timmy-quinn/hid_keyboard/01_FW/src/kb_ble/kb_cent.c

#include <bluetooth/gatt_dm.h>
#include <bluetooth/scan.h>
#include <bluetooth/services/hogp.h>
#include <errno.h>
#include <stddef.h>
#include <zephyr/bluetooth/bluetooth.h>
#include <zephyr/bluetooth/conn.h>
#include <zephyr/bluetooth/gatt.h>
#include <zephyr/bluetooth/hci.h>
#include <zephyr/bluetooth/uuid.h>
#include <zephyr/kernel.h>
#include <zephyr/settings/settings.h>
#include <zephyr/sys/byteorder.h>
#include <zephyr/sys/printk.h>
#include <zephyr/types.h>

#include "kb_cent.h"
#include "kb_hid_common.h"
#include "kb_periph.h"

static struct bt_conn *default_conn;
static struct bt_hogp hogp;
static struct bt_conn *auth_conn;

static void hids_on_ready(struct k_work *work);
static K_WORK_DEFINE(hids_ready_work, hids_on_ready);

static void scan_filter_match(struct bt_scan_device_info *device_info,
                              struct bt_scan_filter_match *filter_match,
                              bool connectable) {
    char addr[BT_ADDR_LE_STR_LEN];

    if (!filter_match->uuid.match ||
        (filter_match->uuid.count != 1)) {
        printk("Invalid device connected\n");

        return;
    }

    const struct bt_uuid *uuid = filter_match->uuid.uuid[0];

    bt_addr_le_to_str(device_info->recv_info->addr, addr, sizeof(addr));

    printk("Filters matched on UUID 0x%04x.\nAddress: %s connectable: %s\n",
           BT_UUID_16(uuid)->val,
           addr, connectable ? "yes" : "no");
}

static void scan_connecting_error(struct bt_scan_device_info *device_info) {
    printk("Connecting failed\n");
}

static void scan_connecting(struct bt_scan_device_info *device_info, struct bt_conn *conn) {
    default_conn = bt_conn_ref(conn);
}
/** .. include_startingpoint_scan_rst */
static void scan_filter_no_match(struct bt_scan_device_info *device_info,
                                 bool connectable) {
    int err;
    struct bt_conn *conn;
    char addr[BT_ADDR_LE_STR_LEN];

    if (device_info->recv_info->adv_type == BT_GAP_ADV_TYPE_ADV_DIRECT_IND) {
        bt_addr_le_to_str(device_info->recv_info->addr, addr,
                          sizeof(addr));
        printk("Direct advertising received from %s\n", addr);
        bt_scan_stop();

        err = bt_conn_le_create(device_info->recv_info->addr,
                                BT_CONN_LE_CREATE_CONN,
                                device_info->conn_param, &conn);

        if (!err) {
            default_conn = bt_conn_ref(conn);
            bt_conn_unref(conn);
        }
    }
}
/** .. include_endpoint_scan_rst */
BT_SCAN_CB_INIT(scan_cb, scan_filter_match, scan_filter_no_match,
                scan_connecting_error, scan_connecting);

static void discovery_completed_cb(struct bt_gatt_dm *dm,
                                   void *context) {
    int err;

    printk("The discovery procedure succeeded\n");

    bt_gatt_dm_data_print(dm);

    err = bt_hogp_handles_assign(dm, &hogp);
    if (err) {
        printk("Could not init HIDS client object, error: %d\n", err);
    }

    err = bt_gatt_dm_data_release(dm);
    if (err) {
        printk(
            "Could not release the discovery data, error "
            "code: %d\n",
            err);
    }
}

static void discovery_service_not_found_cb(struct bt_conn *conn,
                                           void *context) {
    printk("The service could not be found during the discovery\n");
}

static void discovery_error_found_cb(struct bt_conn *conn,
                                     int err,
                                     void *context) {
    printk("The discovery procedure failed with %d\n", err);
}

static const struct bt_gatt_dm_cb discovery_cb = {
    .completed = discovery_completed_cb,
    .service_not_found = discovery_service_not_found_cb,
    .error_found = discovery_error_found_cb,
};

void cent_gatt_discover(struct bt_conn *conn) {
    int err;

    if (conn != default_conn) {
        return;
    }

    err = bt_gatt_dm_start(conn, BT_UUID_HIDS, &discovery_cb, NULL);
    if (err) {
        printk(
            "could not start the discovery procedure, error "
            "code: %d\n",
            err);
    }
}

void cent_connected(struct bt_conn *conn, uint8_t conn_err) {
    int err;
    char addr[BT_ADDR_LE_STR_LEN];

    bt_addr_le_to_str(bt_conn_get_dst(conn), addr, sizeof(addr));

    if (conn_err) {
        printk("Failed to connect to %s (%u)\n", addr, conn_err);
        if (conn == default_conn) {
            bt_conn_unref(default_conn);
            default_conn = NULL;

            /* This demo doesn't require active scan */
            err = bt_scan_start(BT_SCAN_TYPE_SCAN_ACTIVE);
            if (err) {
                printk("Scanning failed to start (err %d)\n",
                       err);
            }
        }

        return;
    }

    printk("Connected: %s\n", addr);

    err = bt_conn_set_security(conn, BT_SECURITY_L2);
    if (err) {
        printk("Failed to set security: %d\n", err);

        cent_gatt_discover(conn);
    }
}

void cent_disconnected(struct bt_conn *conn, uint8_t reason) {
    char addr[BT_ADDR_LE_STR_LEN];
    int err;

    bt_addr_le_to_str(bt_conn_get_dst(conn), addr, sizeof(addr));

    if (auth_conn) {
        bt_conn_unref(auth_conn);
        auth_conn = NULL;
    }

    printk("Disconnected: %s (reason %u)\n", addr, reason);

    if (bt_hogp_assign_check(&hogp)) {
        printk("HIDS client active - releasing");
        bt_hogp_release(&hogp);
    }

    if (default_conn != conn) {
        return;
    }

    bt_conn_unref(default_conn);
    default_conn = NULL;

    /* This demo doesn't require active scan */
    err = bt_scan_start(BT_SCAN_TYPE_SCAN_ACTIVE);
    if (err) {
        printk("Scanning failed to start (err %d)\n", err);
    }
}

static void security_changed(struct bt_conn *conn, bt_security_t level,
                             enum bt_security_err err) {
    char addr[BT_ADDR_LE_STR_LEN];

    bt_addr_le_to_str(bt_conn_get_dst(conn), addr, sizeof(addr));

    if (!err) {
        printk("Security changed: %s level %u\n", addr, level);
    } else {
        printk("Security failed: %s level %u err %d\n", addr, level,
               err);
    }

    cent_gatt_discover(conn);
}

BT_CONN_CB_DEFINE(conn_callbacks) = {
    .connected = cent_connected,
    .disconnected = cent_disconnected,
    .security_changed = security_changed};

static void scan_init(void) {
    int err;

    struct bt_scan_init_param scan_init = {
        .connect_if_match = 1,
        .scan_param = NULL,
        .conn_param = BT_LE_CONN_PARAM_DEFAULT};

    bt_scan_init(&scan_init);
    bt_scan_cb_register(&scan_cb);

    err = bt_scan_filter_add(BT_SCAN_FILTER_TYPE_UUID, BT_UUID_HIDS);
    if (err) {
        printk("Scanning filters cannot be set (err %d)\n", err);

        return;
    }

    err = bt_scan_filter_enable(BT_SCAN_UUID_FILTER, false);
    if (err) {
        printk("Filters cannot be turned on (err %d)\n", err);
    }
}

static uint8_t hogp_notify_cb(struct bt_hogp *hogp,
                              struct bt_hogp_rep_info *rep,
                              uint8_t err,
                              const uint8_t *data) {
    static kb_state_t kb;
    uint8_t size = bt_hogp_rep_size(rep);

    if (!data) {
        return BT_GATT_ITER_STOP;
    }
    if (size != INPUT_REPORT_KEYS_MAX_LEN) {
        // TODO: Not sure if this is proper behavior
        //  Not sure if it should return STOP or CONTINUE
        return BT_GATT_ITER_STOP;
    }

    for (uint8_t i = 0; i < KEY_PRESS_MAX; i++) {
        kb_hid_key_change(kb.keys_state[i], data[i + KEY_OFFSET_IN_REPORT]);
        kb.keys_state[i] = data[i + KEY_OFFSET_IN_REPORT];
    }

    if (kb.ctrl_keys != data[0]) {
        for (uint8_t i = 0; i < 8; i++) {
            kb_hid_key_change(get_ctrl_scan_code(kb.ctrl_keys, i),
                              get_ctrl_scan_code(data[0], i));
        }
    }
    kb.ctrl_keys = data[0];

    kb_periph_hid_notify();
    return BT_GATT_ITER_CONTINUE;
}

static uint8_t hogp_boot_kbd_report(struct bt_hogp *hogp,
                                    struct bt_hogp_rep_info *rep,
                                    uint8_t err,
                                    const uint8_t *data) {
    uint8_t size = bt_hogp_rep_size(rep);
    uint8_t i;

    if (!data) {
        return BT_GATT_ITER_STOP;
    }
    printk("Notification, keyboard boot, size: %u, data:", size);
    for (i = 0; i < size; ++i) {
        printk(" 0x%x", data[i]);
    }
    printk("\n");

    return BT_GATT_ITER_CONTINUE;
}

static void hogp_ready_cb(struct bt_hogp *hogp) {
    k_work_submit(&hids_ready_work);
}

static void hids_on_ready(struct k_work *work) {
    int err;
    struct bt_hogp_rep_info *rep = NULL;

    printk("HIDS is ready to work\n");

    while (NULL != (rep = bt_hogp_rep_next(&hogp, rep))) {
        if (bt_hogp_rep_type(rep) ==
            BT_HIDS_REPORT_TYPE_INPUT) {
            printk("Subscribe to report id: %u\n",
                   bt_hogp_rep_id(rep));
            err = bt_hogp_rep_subscribe(&hogp, rep,
                                        hogp_notify_cb);
            if (err) {
                printk("Subscribe error (%d)\n", err);
            }
        }
    }
    if (hogp.rep_boot.kbd_inp) {
        printk("Subscribe to boot keyboard report\n");
        err = bt_hogp_rep_subscribe(&hogp,
                                    hogp.rep_boot.kbd_inp,
                                    hogp_boot_kbd_report);
        if (err) {
            printk("Subscribe error (%d)\n", err);
        }
    }
    if (hogp.rep_boot.mouse_inp) {
        printk("ERROR: device found is mouse not keyboard\n");
        // err = bt_hogp_rep_subscribe(&hogp,
        // 				   hogp.rep_boot.mouse_inp,
        // 				   hogp_boot_mouse_report);
        // if (err) {
        // 	printk("Subscribe error (%d)\n", err);
        // }
    }
}

static void hogp_prep_fail_cb(struct bt_hogp *hogp, int err) {
    printk("ERROR: HIDS client preparation failed!\n");
}

static void hogp_pm_update_cb(struct bt_hogp *hogp) {
    printk("Protocol mode updated: %s\n",
           bt_hogp_pm_get(hogp) == BT_HIDS_PM_BOOT ? "BOOT" : "REPORT");
}

/* HIDS client initialization parameters */
static const struct bt_hogp_init_params hogp_init_params = {
    .ready_cb = hogp_ready_cb,
    .prep_error_cb = hogp_prep_fail_cb,
    .pm_update_cb = hogp_pm_update_cb};

// TODO: Use this to switch keyboard from boot mode to report mode.
static void button_bootmode(void) {
    if (!bt_hogp_ready_check(&hogp)) {
        printk("HID device not ready\n");
        return;
    }
    int err;
    enum bt_hids_pm pm = bt_hogp_pm_get(&hogp);
    enum bt_hids_pm new_pm = ((pm == BT_HIDS_PM_BOOT) ? BT_HIDS_PM_REPORT : BT_HIDS_PM_BOOT);

    printk("Setting protocol mode: %s\n", (new_pm == BT_HIDS_PM_BOOT) ? "BOOT" : "REPORT");
    err = bt_hogp_pm_write(&hogp, new_pm);
    if (err) {
        printk("Cannot change protocol mode (err %d)\n", err);
    }
}

static void num_comp_reply(bool accept) {
    if (accept) {
        bt_conn_auth_passkey_confirm(auth_conn);
        printk("Numeric Match, conn %p\n", auth_conn);
    } else {
        bt_conn_auth_cancel(auth_conn);
        printk("Numeric Reject, conn %p\n", auth_conn);
    }

    bt_conn_unref(auth_conn);
    auth_conn = NULL;
}

void cent_pairing_accept() {
    num_comp_reply(true);
}

void cent_auth_passkey_confirm(struct bt_conn *conn, unsigned int passkey) {
    char addr[BT_ADDR_LE_STR_LEN];

    auth_conn = bt_conn_ref(conn);

    bt_addr_le_to_str(bt_conn_get_dst(conn), addr, sizeof(addr));

    printk("Passkey for %s: %06u\n", addr, passkey);
    printk("Press Button 1 to confirm, Button 2 to reject.\n");
}

void cent_pairing_failed(struct bt_conn *conn, enum bt_security_err reason) {
    char addr[BT_ADDR_LE_STR_LEN];

    bt_addr_le_to_str(bt_conn_get_dst(conn), addr, sizeof(addr));

    printk("Pairing failed conn: %s, reason %d\n", addr, reason);
}

void kb_cent_scan_start() {
    int err;
    err = bt_scan_start(BT_SCAN_TYPE_SCAN_ACTIVE);
    if (err) {
        printk("Scanning failed to start (err %d)\n", err);
        return;
    }

    printk("Scanning successfully started\n");
}

void kb_cent_init(void) {
    bt_hogp_init(&hogp, &hogp_init_params);
    scan_init();
}
