timmy-quinn/hid_keyboard/01_FW/src/kb_ble/kb_periph.h

#ifndef KB_BLE_PERIPHERAL
#define KB_BLE_PERIPHERAL

#include <zephyr/bluetooth/conn.h>

#include "kb_hid_common.h"

void periph_auth_passkey_confirm(struct bt_conn *conn, unsigned int passkey);
void periph_pairing_failed(struct bt_conn *conn, enum bt_security_err reason);

void periph_connected(struct bt_conn *conn, uint8_t err);
void periph_disconnected(struct bt_conn *conn, uint8_t reason);

void kb_periph_hid_notify();
void kb_periph_bas_notify(void);

void kb_periph_adv_start(void);
void kb_periph_accept_pairing();
void kb_periph_init(void);

bool kb_periph_is_adv();
#endif
